0b1-k/humble-roots-project-lua/weed/dashboard/grafana/dash-drying-mode.png

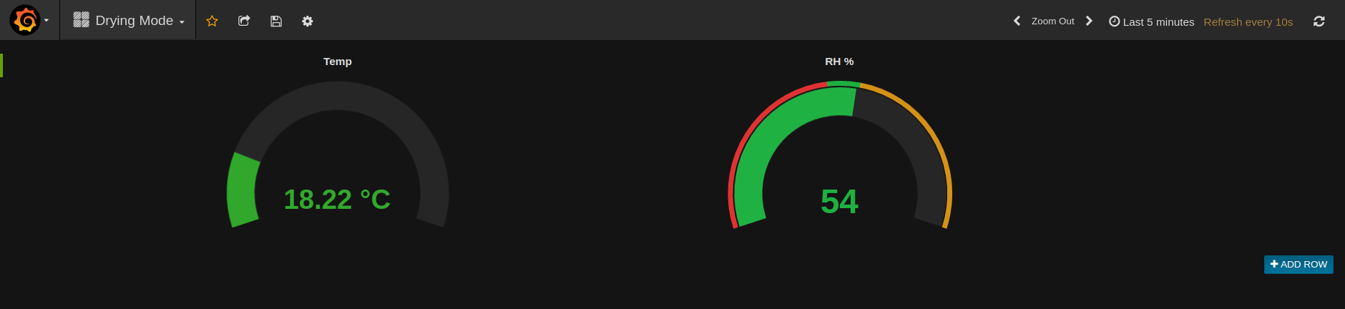
weed/dashboard/grafana/dash-drying-mode.png
