0b1-k/humble-roots-project-lua/weed/dashboard/grafana/dash.png

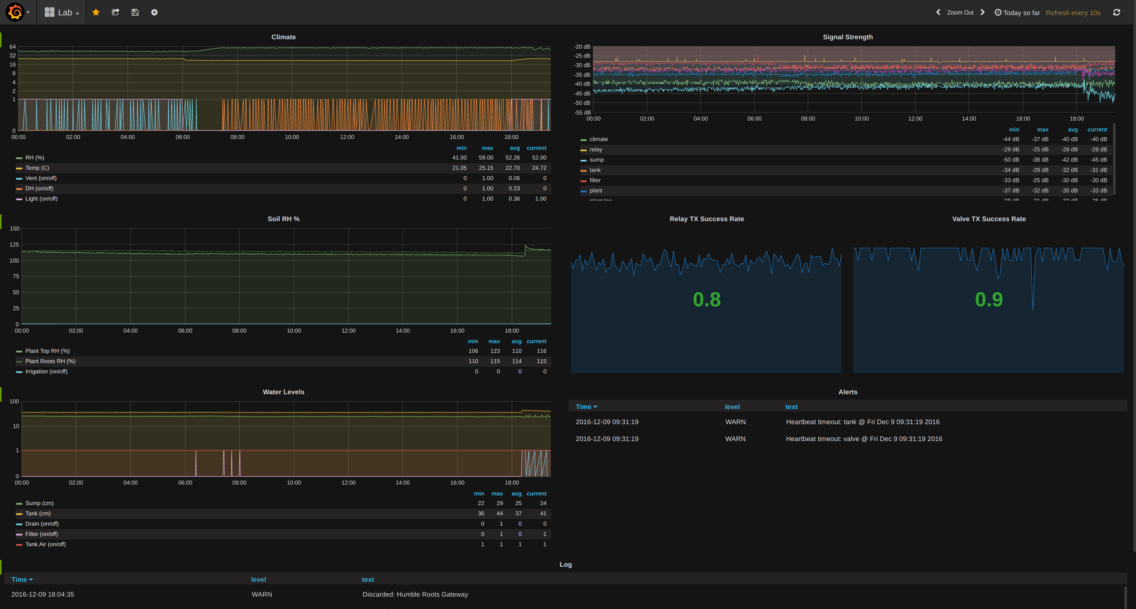
weed/dashboard/grafana/dash.png
