0b1-k/humble-roots-project-lua/weed/pics/EG1.1.JPG

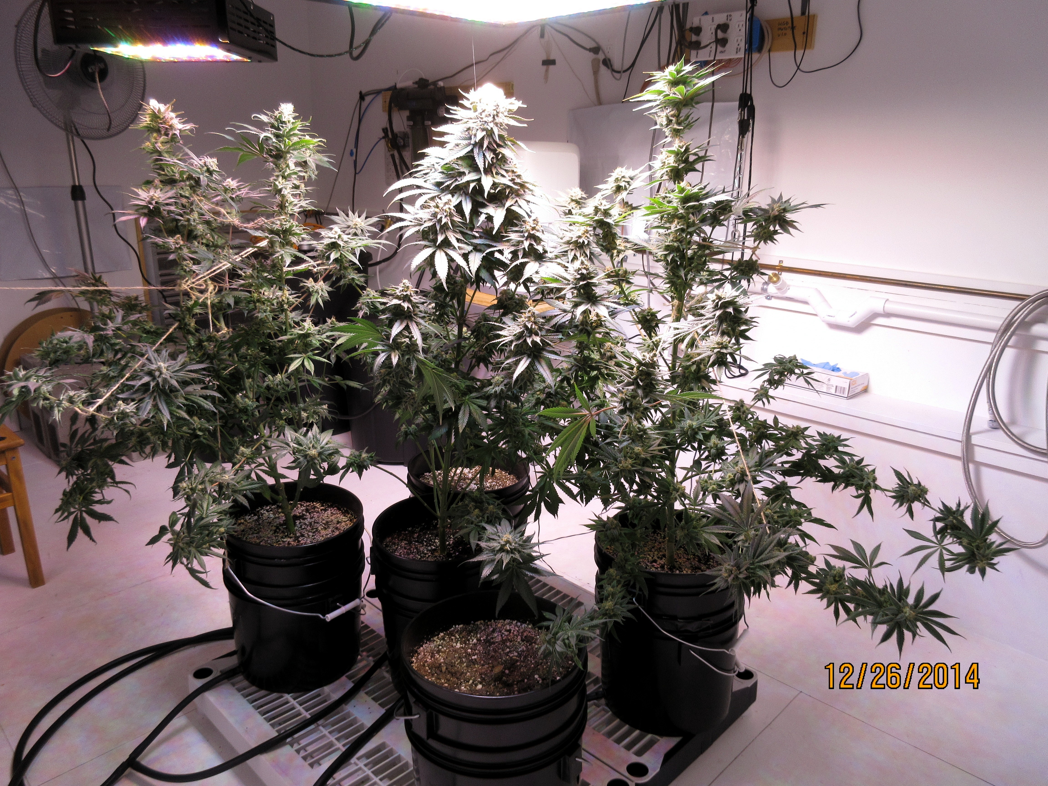
weed/pics/EG1.1.JPG
