0b1-k/humble-roots-project-lua/weed/pics/EG2.4.JPG

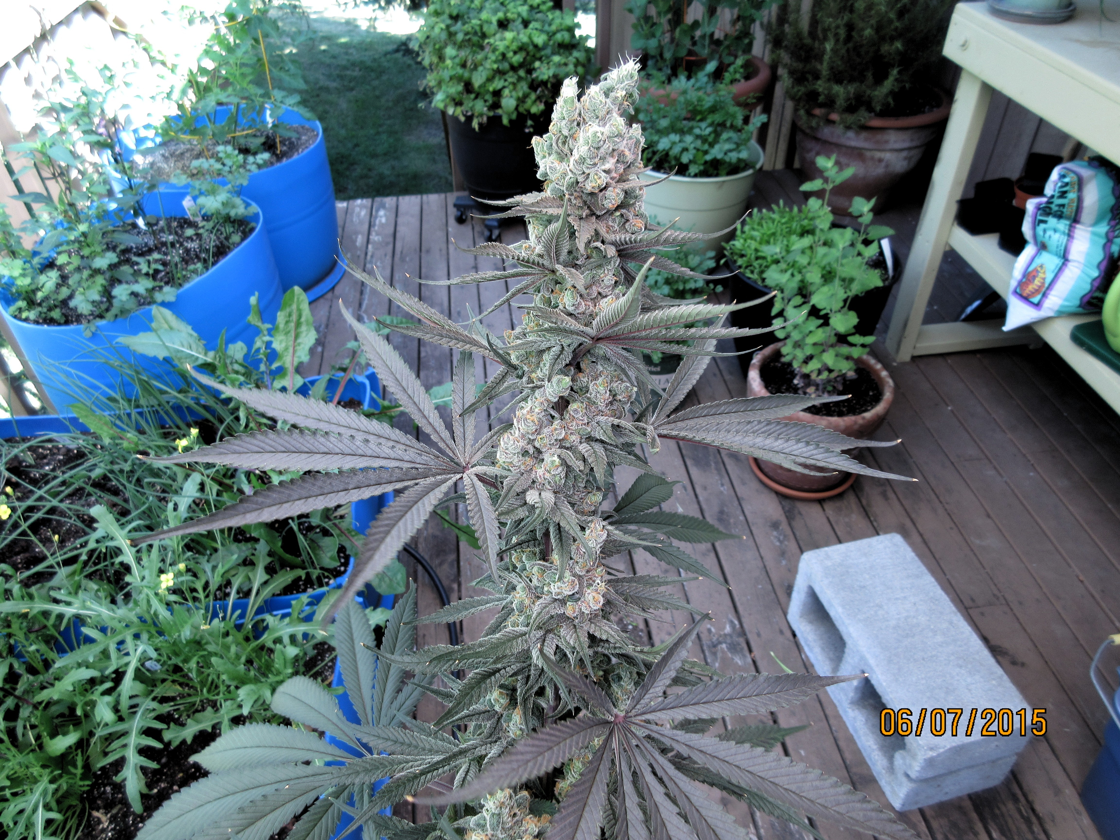
weed/pics/EG2.4.JPG
