0b1-k/humble-roots-project-lua/weed/pics/EG2.6.JPG

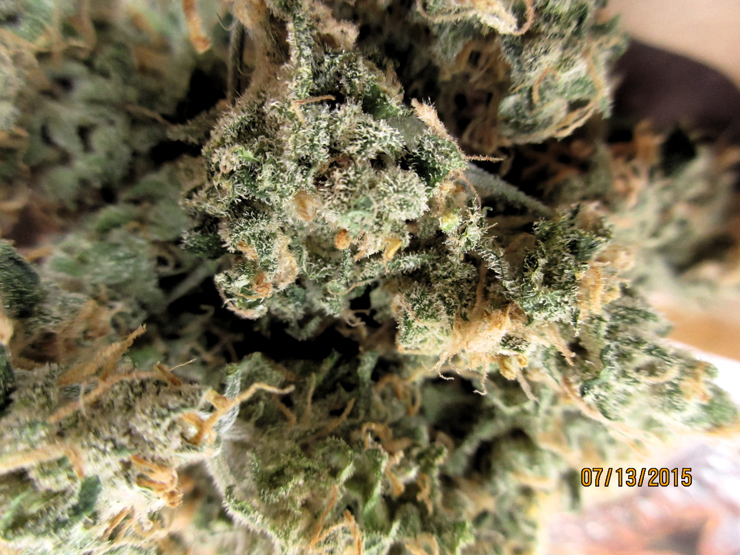
weed/pics/EG2.6.JPG
