0b1-k/humble-roots-project-lua/weed/pics/EG2.8.JPG

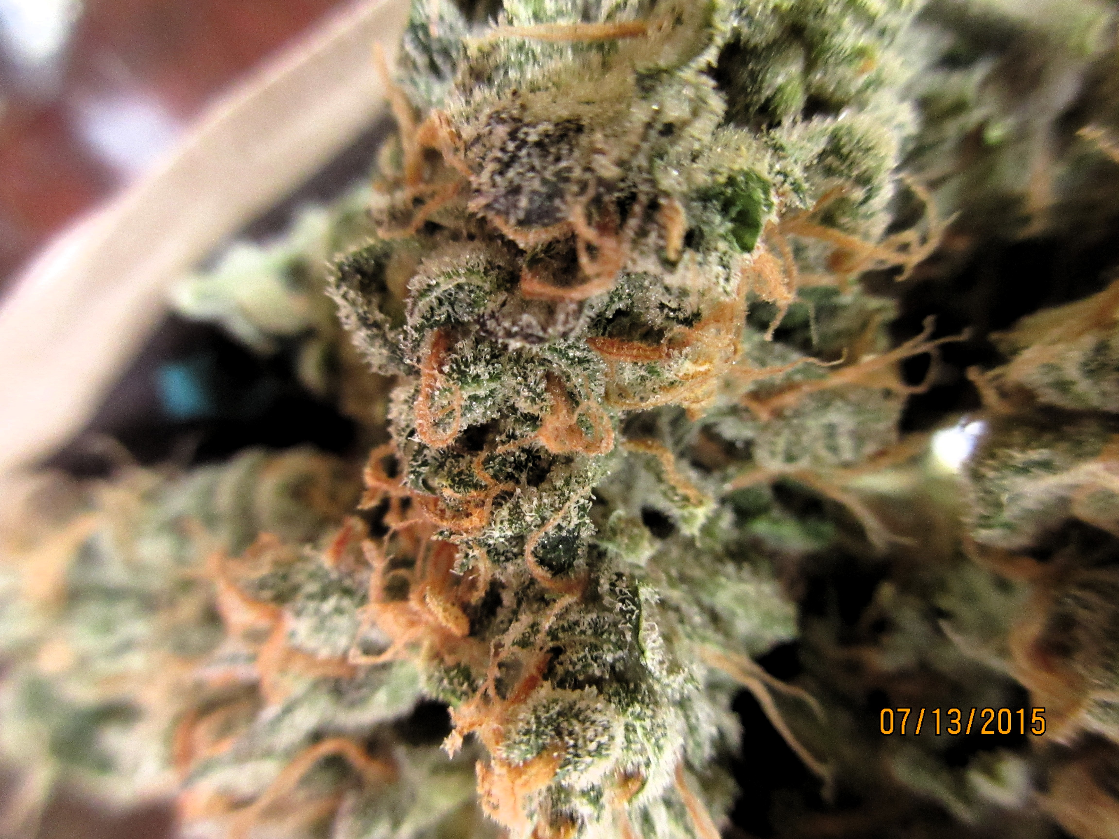
weed/pics/EG2.8.JPG
