0b1-k/humble-roots-project-lua/weed/pics/EG2.9.JPG

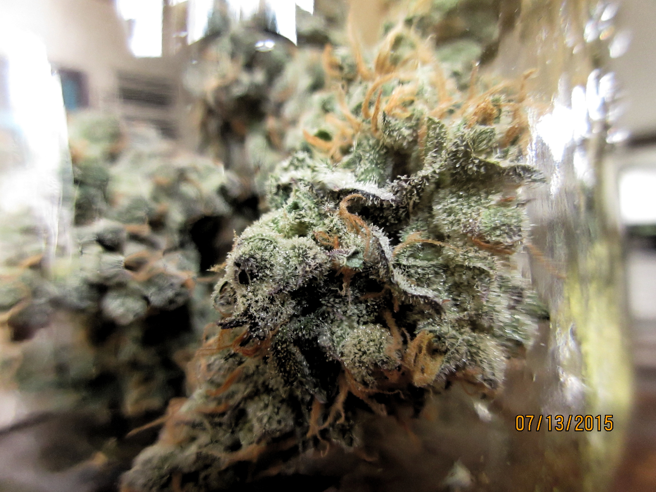
weed/pics/EG2.9.JPG
