0b1-k/humble-roots-project-lua/weed/pics/EG2.seeds.jpg

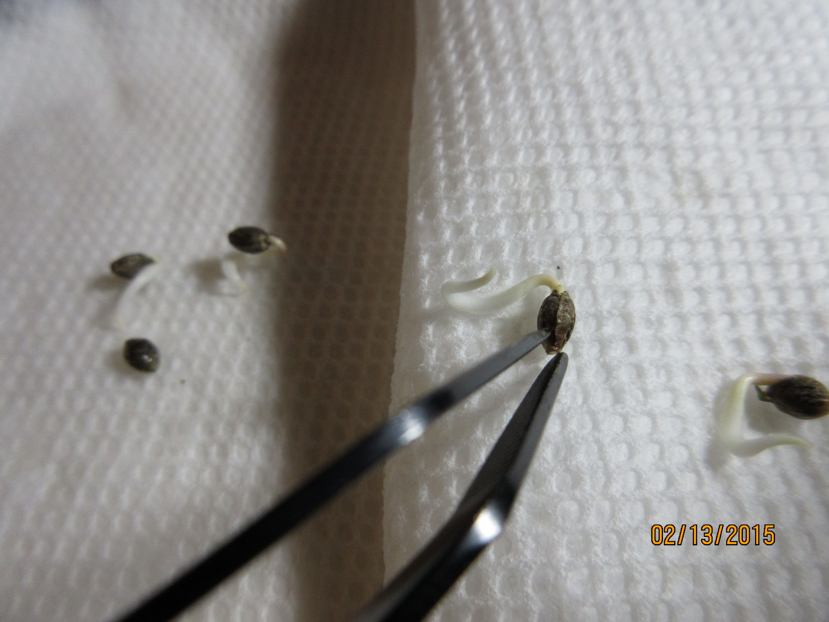
weed/pics/EG2.seeds.jpg
