0b1-k/humble-roots-project-lua/weed/pics/GDP.TW.JPG

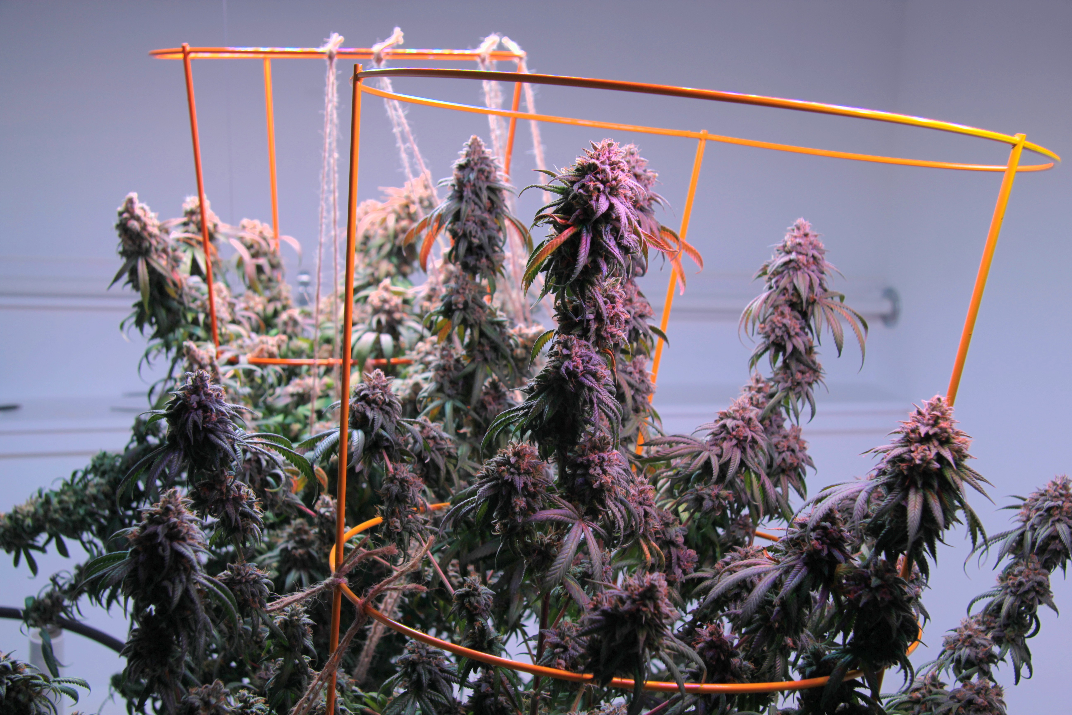
weed/pics/GDP.TW.JPG
