0b1-k/humble-roots-project-lua/weed/pics/TW.0.JPG

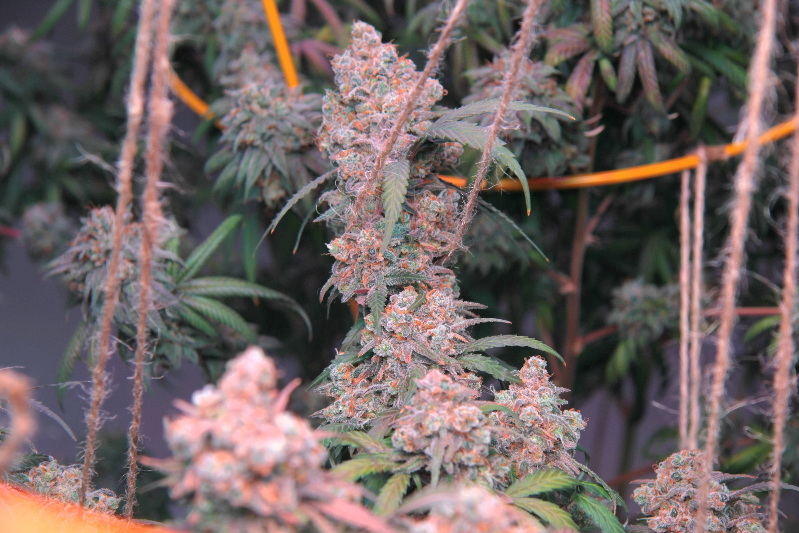
weed/pics/TW.0.JPG
