0b1-k/humble-roots-project-lua/weed/pics/WR.0.jpg

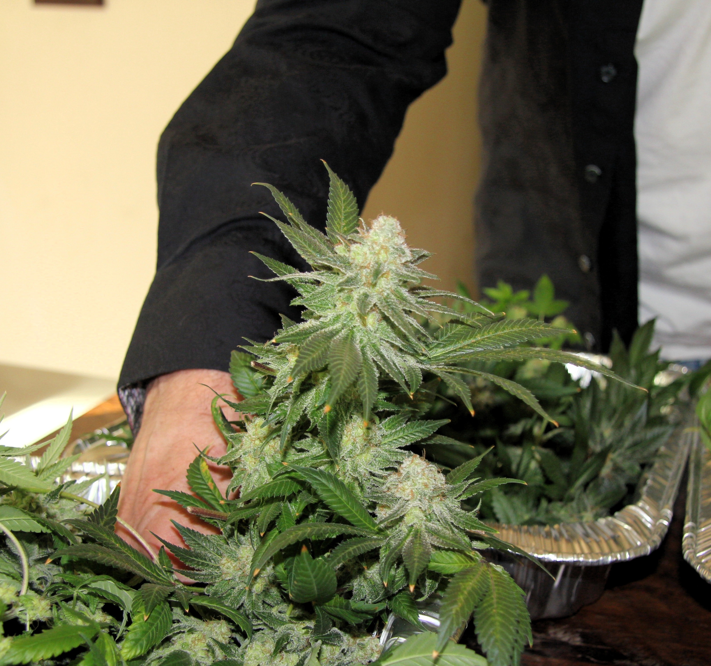
weed/pics/WR.0.jpg
