0b1-k/humble-roots-project-lua/weed/listener.lua

local socket = require("socket")
local log = _ENV.log

local server = 0

local function initialize(bind, portNum)
  local err = 0
  server, err = socket.bind(bind, portNum)
  if server == nil then
    log.error(string.format("Failed to bind: %s", err))
    return
  end
  server:settimeout(0.01)
  local ip, port = server:getsockname()
  log.info(string.format("Shell listening @ %s:%s", ip, port))
end

local function receive(onShellMsg)
  if server == nil then
    return nil
  end
  local client = server:accept()
  if client ~= nil then
    client:settimeout(0.100)
    local line, err = client:receive()
    if not err then
      local resp = onShellMsg(line)
      if resp ~= nil then
        client:send(resp)
      end
    end
    client:close()
  end
end

local function shutdown()
  if server ~= nil then
    server:close()
  end
end

local export = {}
export.initialize = initialize
export.receive = receive
export.shutdown = shutdown
return export
