0b1-k/humble-roots-project-lua/weed/heartbeat.lua

local sms = require("sms")
local log = _ENV.log

local nodes = {}
local cfg = {}

local function initialize(config)
  nodes = {}
  cfg = config
  for k, _ in pairs(cfg.node) do
    local isNodeId = tonumber(k)
    if isNodeId == nil then -- got a node name
      local timeoutObj = {}
      timeoutObj.nodeTimeout = cfg.control.nodeTimeout.freqSec
      timeoutObj.rebootTimeout = cfg.control.nodeTimeout.rebootAfter
      nodes[k] = timeoutObj
    end
  end
end

local function composeAlert(nodeName, clear)
  local mark = ""
  if clear then
    mark = cfg.alerts.clear
  else
    mark = cfg.alerts.raise
  end
  return string.format("[%s] %s %s @ %s", nodeName, cfg.control.nodeTimeout.title, mark, os.date("%c", os.time()))
end

local function elapseTime(seconds)
  for node, _ in pairs(nodes) do
    local timeoutObj = nodes[node]
    if timeoutObj.nodeTimeout > 0 then
      timeoutObj.nodeTimeout = timeoutObj.nodeTimeout - seconds
      if timeoutObj.nodeTimeout <= 0 then
        timeoutObj.rebootTimeout = (cfg.control.nodeTimeout.rebootAfter - cfg.control.nodeTimeout.freqSec)
        local alertMsg = composeAlert(node, false)
        sms.send(cfg, alertMsg)
        log.warn(alertMsg)
      end
      nodes[node] = timeoutObj
    else
      if cfg.control.nodeTimeout.reboot then
        local alertMsg = string.format("[%s] %s @ %s", node, cfg.control.nodeTimeout.rebootMsg, os.date("%c", os.time()))
        sms.send(cfg, alertMsg)
        log.fatal(alertMsg)
        os.execute(cfg.control.nodeTimeout.rebootCmd)
      end
    end
  end
end

local function pulse(node)
  local timeoutObj = nodes[node]
  if timeoutObj ~= nil then
    if timeoutObj.nodeTimeout <= 0 then
      local alertMsg = composeAlert(node, true)
      sms.send(cfg, alertMsg)
      log.warn(alertMsg)
    end
    timeoutObj.nodeTimeout = cfg.control.nodeTimeout.freqSec
    timeoutObj.rebootTimeout = cfg.control.nodeTimeout.rebootAfter
    nodes[node] = timeoutObj
  end
end

local export = {}
export.initialize = initialize
export.elapseTime = elapseTime
export.pulse = pulse
return export
