0b1-k/humble-roots-project-lua/weed/pics/EG2.7.JPG

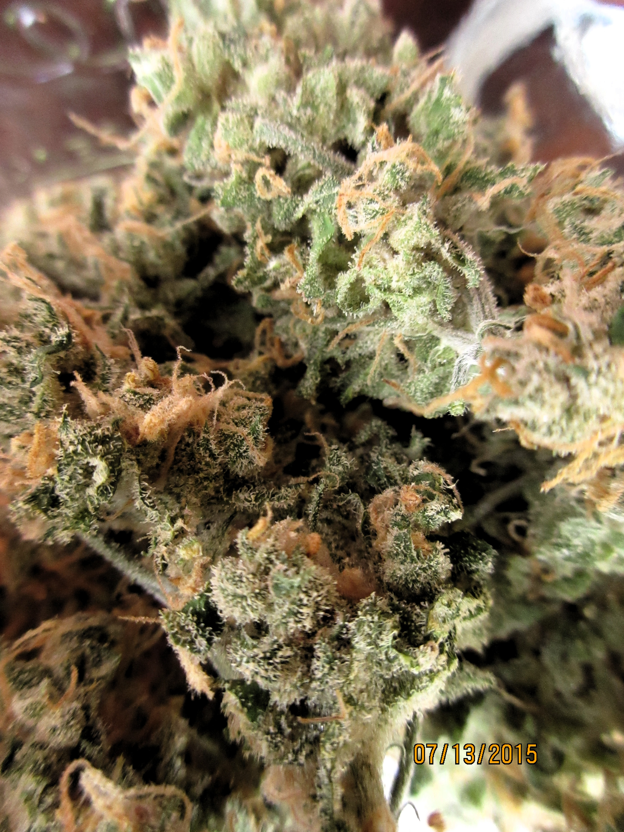
weed/pics/EG2.7.JPG
